SvOlli/sorbus/doc/site/jam/monitors.md

# Monitors

Not displays are meant here, but software that allows you to view and change
the content of memory. And most of the times, more.

## WozMon

Storage: in ROM

The most basic one, implemented originally in just 256 bytes for the Apple 1
Computer. Everything is entered and displayed as hex.

Available commands (examples):

- `0400`: dump the content of memory location $0400
- `0400 0404`: dump the content of memory locations $0400 and $0404
- `0400.0407`: dump the content of memory locations $0400 to $0407
- `0400: 9C`: write $9C to memory location $0400
- `0400: 9C 01 DF A0 00 00 09 60`: write the bytes to memory starting at $0400
- `0400R`: start the program $0400 (an alias `0400G` can be used as well)

A significant change to the Sorbus version of WozMon is that if a routine
started using the `R` command returns using the `RTS` opcode will drop you
back to WozMon. This is also the final ballback if everything else fails
(NMOS 6502 CPU installed and no software available on bootblock 2).

## TIM

TIM (Terminal Interface Monitor) is a small (1kB) program that was part of the
MOS 6530-004 chip. That chip was sold together with the first 6502 CPUs and
documentation on how to build a computer with this. Also this chip is used in
the Jolt Computer, which was the first computer sold based on the 6502.

The following descriptions lacks description of the paper tape and other I/O
routines, besides mentioning them.

Output: upon start you are typically greeted with

```txt
    ADDR P  A  X  Y  S
 *  E619 33 28 00 00 FF
.
```

The first line is an addition by the Sorbus version of TIM to help
understanding the output below:

- The first char indicates the kind of interrupt that occured:
  - ` ` (space): BRK instruction (BRK #$00 on Sorbus, since it's implemented
    as a two byte instruction
  - `#` (hash): NMI triggered via $FFFA/$FFFB
  - `%` (percent): IRQ triggered via $FFFE/$FFFF (Sorbus extension)
- `*` always printed
- ADDR: current address. The monitor is typically triggered by an interrupt.
- P: processor flags
- A: accumulator
- X: index register X
- Y: index register Y
- S: stack pointer (full stack pointer value is $01xx)

The following dot (`.`) is the input prompt. Note that there is no backspace
available. The input needs to be canceled and then start anew.

Available commands:

- `M`: dump 8 bytes of memory
- `R`: dump registers (the line described above)
- `:`: change the former output data
- `G`: go to the address shown in ADDR
- `L`, `W`, `H`: these are related to paper tape
- `V`: enables/disables verify for the `LH` command

So jumping to a specific address is handled by first running `R`, then changing
the ADDR with `:` (you can skip the rest by pressing return), and finally jump
using `G`. However, to return to the monitor you have to invoke it again using
the `BRK $00` opcode, `RTS` will not work here, like it did in WozMon.

A more detailed documentation is at the start of the
TIM source code (src/65c02/jam/rom/tim.s). The following is a revised version.

```txt
PROMPTING CHARACTER IS A PERIOD (.)
-----------------------------------

DISPLAY COMMANDS
----------------

.R                   DISPLAY REGISTERS (PC,F,A,X,Y,SP)
.M  ADDR             DISPLAY MEMORY ( 8 BYTES BEGINNING AT ADDR )

ALTER COMMAND (:)
-----------------
.:  DATA             ALTERS PREVIOUSLY DISPLAYED ITEM OR NEXT ITEM

PAPER TAPE I/O COMMANDS
------------------------

.LH                  LOAD HEX TAPE
.WB ADDR1 ADDR2      WRITE BNPF TAPE (FROM LOW ADDR1 TO HIGH ADDR2)
.WH ADDR1 ADDR2      WRITE HEX TAPE (FROM LOW ADDR1 TO HIGH ADDR2)

CONTROL COMMANDS
----------------

.G                   GO, CONTINUE EXECUTION FROM CIRRENT PC ADDRESS

.V                   TOGGLES VERIFY OPTION (DEFAULT: OFF)
                        (IF ITS ON, TURNS IT OFF; IF OFF, TURNS ON)

BRK AND NMI ENTRY POINTS TO TIM
-------------------------------

    TIM IS NORMALLY ENTERED WHEN A 'BRK' INSTRUKTION IS
        ENCOUNTERED DURING PROGRAM EXECUTION.  AT THAT
        TIME CPU REGISTERS ARE OUTPUT:    PC F A X Y SP
        and   CONTROL   IS GIVEN TO THE KEYBOARD.

    USER MAY ENTER TIM BY PROGRAMMED BRK OR INDUCED NMI.  NMI
        ENTRIES CAUSE A '#' TO PRECEDE THE '.' IN THE CPU REGISTER
        PRINTOUT FORMAT

NON-BRK INTRO (EXTERNAL DEVICE) INTERRUPT HANDLING
--------------------------------------------------

    A NON-BRK INTRO INTERRUPT CAUSES AN INDIRECT JUMP TO THE ADDRESS
        LOCATED AT 'UINT' (HEX FFF8).  THIS LOCATION CAN BE SET
        USING THE ALTER CMD, OR LOADED AUTOMATICALLY IN PAPER TAPE
        FROM WITH THE LH CMD IF THE USER ASSIGNS HIS INTRO INTERRUPT
        VECTOR TO $FFF8 IN THE SOURCE ASSEMBLY PROGRAM.

    IF NOT RESET BY THE USER, UINT IS SET TO CAUSE EXTERNAL
        DEVICE INTERRUPTS TO ENTER TIM AS NMI'S.  I.E.,
        IF A NMI OCOURS WITHOUT AN INDUCED NMI SIGNAL, IT IS
        AN EXTERNAL DEVICE INTERRUPT.

    Note: This has been changed for Sorbus from FFF8 to DF7C (UBRK)

SETTING AND RESETTING PROGRAM BREAKPOINTS
-----------------------------------------

    BREAKPOINTS ARE SET AND RESET USING THE MEMORY DISPLAY
        AND ALTER COMMANDS.  BRK HAS A '00' OPERATION CODE.
    TO SET A BREAKPOINT SIMPLY DISPLAY THE MEMORY LOCATION
        (FIRST INSTRUCTION.byte) AT WHICH THE BREAKPOINT IS
        TO BE PLACED THEN ALTER THE LOCATION TO '00'.  THERE IS
        NO LIMIT TO THE NUMBER OF BREAKPOINTS THAT CAN BE
        ACTIVE AT ONE TIME.
    TO RESET A BREAKPOINT, RESTORE THE ALTERED MEMORY LOCATION
        TO ITS ORIGINAL VALUE.
    WHEN AND IF A BREAKPOINT IS ENCOUNTERED DURING EXECUTION,
        THE BREAKPOINT DATA PRECEDEC BY AN ':' IS DISPLAYED.
        THE PROGRAM COUNTER VALUE DISPLAYED IS THE BRK
        INSTRUCTION LOCATION + 1.
```

### Loading Software Via Papertape

Papertape was a common way of getting data into the first microcomputers.
Typically you set the machine into some kind of receiving mode and then
switched the input to the papertape. For the machine it was like someone
was typing in the data really fast.

Format of papertape data is:

```txt
;CCAAAADD[DD..]SSSS
```

Every character (except for the semicolon) stands for a hex digit.

| Byte | Function |
| ---- | --- |
| ; | indication of papertape data |
| CC | number of databytes sent later on, 00 indicates end of transmission |
| AAAA | address to write to |
| DD | a byte of data, number of bytes must match the number specified as CC |
| SSSS | checksum, every byte of CC, AA (2 bytes) and DD are added up and must match SSSS  |

The implementation is in TIM is rather fast. When using 32 bytes chunks
of data, you can load about 2kB per second.

## System Monitor of Apple //c (WozMon 2c)

Storage: as loadable program.

This monitor is a very enhanced version of the original WozMon, now
utilizing about 1.5k bytes without the help message. But for this it
comes with a lot of new features like a disassembler, a direct mini
assembler from the Apple //c and file access which is custom to the
Sorbus Computer.

As of now, this monitor needs to be loaded from the internal drive
using the file browser, because it's the monitor with the steepest
learning curve. It is just added to experience how cumbersome it is to
use this monitor.

Displaying and entering data works the same as on the original WozMon.
There is an addition: instead of entering hex data, you can also enter
ASCII by prepending the letter with a single quote (`'`). However, when
entering multiple data, make sure that every letter is prepended with a
quote, and also that the input is separated by spaces.

Furthermore, the `R` command has been renamed to `G` for "go".

All implemented commands (examples):

When the prompt is a asterisk (`*`):

- `0400`: dump the content of memory location $0400
- `0400 0404`: dump the content of memory locations $0400 and $0404
- `0400.0407`: dump the content of memory locations $0400 to $0407
- `0400: 9C`: write $9C to memory location $0400
- `0400: 9C 0D 03 A0 00 00 09 60`: write the bytes to memory starting at $0400
- `0410: 20 06 FF 'H 'e 'l 'l 'o 'r 'l 'd '! 00 60`:
   write a small program that outputs "Hellorld!". Greetings to Usage Electric.
- `0400G`: start the program $0400
- `50+50`: add those to hex values, getting $A0
- `30-22`: subtract those to hex values, getting $0E
- `R`: print out the CPU shadow registers of A, X, Y, P and SP. These will
   be read when using `G` and saved to then the program exists with an `RTS`
   opcode. (Option renamed from Ctrl-E.) The values of those registers can
   be changed by the `:` command as the edit address pointer has been put to
   the correct place in memory ($00FB-$00FF).
- `c000<0400.0bffM`: move (or rather copy) the memory from $0400 to $0BFF to
   $C000 to $C7FF.
- `c000<0400.0bffV`: verify (or rather compare) the memory from $0400 to
   $0BFF to $C000 to $C7FF.
- `bd<c000.cfffP`: put (or rather fill) the memory from $C000 to $CFFF with
   the value of $BD.
- `0400L`: list (or rather disassemble) 20 instructions starting at $0400.
- `!`: drop to the direct mini assembler (see below)
- `A$`: display the directory of the user id $A (10) (Sorbus extension)
- `A<1000{int-test.sx4`: load the file "int-test.sx4" from user id $A (10)
   to address $1000.
- `2<1000.1FFF}savetest.bin`: load the file "savetest.bin" from user id $2
   (2) from address $1000 to $1FFF, including.

When the prompt is an exclamation mark (`!`), the direct mini assembler is
running. Now the user input is evaluated like:

- `1000:stz $DF01`: assemble the instruction `STZ $DF01` to address $1000.
   (Note the `$` is optional.)
- ` rts`: assemble the instruction `RTS` to the now current address.
   ($1003 in this example, also note the mendatory leading space character
   for this case.)
- an empty input returns to the "asterisk input"

The supported instruction set is of the 65SC02. The BRK instruction is not
supporing an operand here, as it is used with the Sorbus JAM kernel.
