SvOlli/sorbus/doc/images/system_clock.png

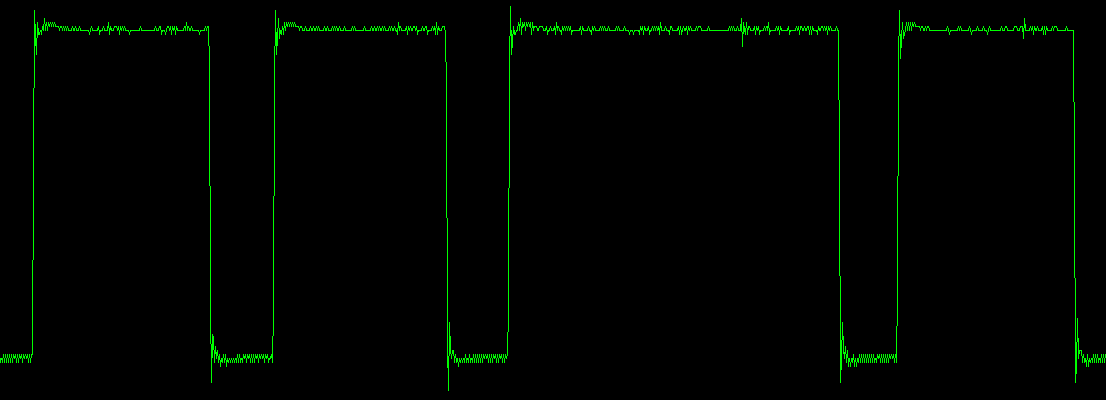
doc/images/system_clock.png
