SvOlli/sorbus/doc/site/images/SorbusPlant.jpg

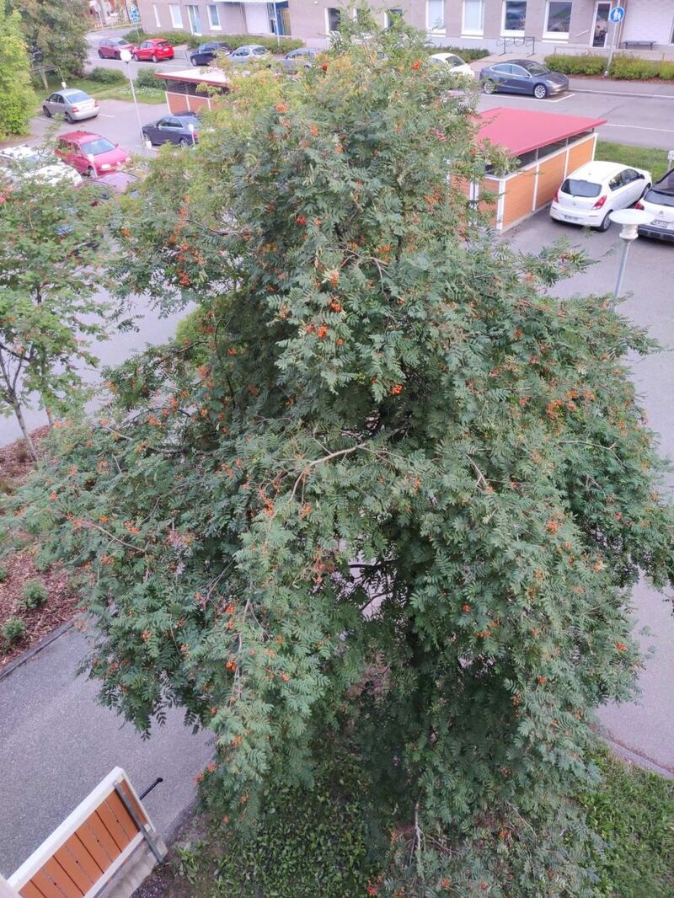
doc/site/images/SorbusPlant.jpg
