SvOlli/sorbus/src/rp2040/vga-term/pmhid.h

/*
 *  KEYCODE to Ascii Conversion
 *
 *  This file contains the various Keyboard Layout declaration supported by
 *  PicoTerm.
 *
 *  Expand to array of [128][3]
 *                       |   +-> (ascii without shift, ascii with shift, ascii with right alt)
 *                       +-----> HID_KEYCODE (0..127)
 *
 * Usage: example to convert ascii from keycode (key) and shift modifier (shift).
 * Here we assume key < 128 ( printable )
 *
 *  uint8_t const conv_table[128][2] =  { HID_KEYCODE_TO_ASCII };
 *  char ch = shift ? conv_table[chr][1] : conv_table[chr][0];
 *
*/

#ifndef _PM_HID_H_
#define _PM_HID_H_

#include "tusb_common.h"

// Choose the mapping @ "make" call (eg: make picoterm, make picoterm_US, make all)
// See CMakeLists.txt for more informations
// Copy and paste an existing mapping to make a new one, see the


#ifdef __cplusplus
 extern "C" {
#endif

#define SCANCODE_F1  0x3a
#define SCANCODE_F2  0x3b
#define SCANCODE_F3  0x3c
#define SCANCODE_F4  0x3d
#define SCANCODE_F5  0x3e
#define SCANCODE_F6  0x3f
#define SCANCODE_F7  0x40
#define SCANCODE_F8  0x41
#define SCANCODE_F9  0x42
#define SCANCODE_F10 0x43
#define SCANCODE_F11 0x44
#define SCANCODE_F12 0x45

#define SCANCODE_CURSOR_LEFT  0x50
#define SCANCODE_CURSOR_RIGHT 0x4F
#define SCANCODE_CURSOR_UP    0x52
#define SCANCODE_CURSOR_DOWN  0x51
#define SCANCODE_PAGE_DOWN    0x4E
#define SCANCODE_PAGE_UP      0x4B
#define SCANCODE_HOME         0x4A
#define SCANCODE_END          0x4D
#define SCANCODE_DEL          0x4C
#define SCANCODE_INS          0x49

// Define esc sequence for some special key-code
#define PM_ESC_SEQ_COUNT 10
#define PM_ESC_SEQ_MAX_LEN 4 /* max len of ESC SEQ (structure make 2 byte more per entry) */
/* Structure: scancode, len_of_sequence, sequence_bytes_(padded_with_NULL) */
#define PM_KEYCODE_TO_ESC_SEQ \
    { SCANCODE_CURSOR_LEFT  , 3, 0x1b,0x5b,0x44,0x00 } /* ESC[D */ , \
		{ SCANCODE_CURSOR_RIGHT , 3, 0x1b,0x5b,0x43,0x00 }, \
    { SCANCODE_CURSOR_UP    , 3, 0x1b,0x5b,0x41,0x00 }, \
    { SCANCODE_CURSOR_DOWN  , 3, 0x1b,0x5b,0x42,0x00 }, \
		{ SCANCODE_PAGE_DOWN    , 4, 0x1b,0x5b,0x36,0x7e } /* ESC[6~ */ , \
    { SCANCODE_PAGE_UP      , 4, 0x1b,0x5b,0x35,0x7e } /* ESC[5~ */ , \
		{ SCANCODE_HOME         , 4, 0x1b,0x5b,0x31,0x7e } /* ESC[1~ */ , \
		{ SCANCODE_END          , 4, 0x1b,0x5b,0x34,0x7e } /* ESC[4~ */ , \
		{ SCANCODE_DEL          , 4, 0x1b,0x5b,0x33,0x7e } /* ESC[3~ */ , \
		{ SCANCODE_INS          , 4, 0x1b,0x5b,0x32,0x7e } /* ESC[2~ */


//--------------------------------------------------------------------/
// US keyboard
//--------------------------------------------------------------------/


#ifdef LOCALISE_US
#define KEYMAP "US"
#define KEYMAP_REV 1
#define PM_KEYCODE_TO_ASCII    \
    {0     , 0     ,0 }, /* 0x00 */ \
    {0     , 0     ,0 }, /* 0x01 */ \
    {0     , 0     ,0 }, /* 0x02 */ \
    {0     , 0     ,0 }, /* 0x03 */ \
    {'a'   , 'A'   ,0 }, /* 0x04 */ \
    {'b'   , 'B'   ,0 }, /* 0x05 */ \
    {'c'   , 'C'   ,0 }, /* 0x06 */ \
    {'d'   , 'D'   ,0 }, /* 0x07 */ \
    {'e'   , 'E'   ,0 }, /* 0x08 */ \
    {'f'   , 'F'   ,0 }, /* 0x09 */ \
    {'g'   , 'G'   ,0 }, /* 0x0a */ \
    {'h'   , 'H'   ,0 }, /* 0x0b */ \
    {'i'   , 'I'   ,0 }, /* 0x0c */ \
    {'j'   , 'J'   ,0 }, /* 0x0d */ \
    {'k'   , 'K'   ,0 }, /* 0x0e */ \
    {'l'   , 'L'   ,0 }, /* 0x0f */ \
    {'m'   , 'M'   ,0 }, /* 0x10 */ \
    {'n'   , 'N'   ,0 }, /* 0x11 */ \
    {'o'   , 'O'   ,0 }, /* 0x12 */ \
    {'p'   , 'P'   ,0 }, /* 0x13 */ \
    {'q'   , 'Q'   ,0 }, /* 0x14 */ \
    {'r'   , 'R'   ,0 }, /* 0x15 */ \
    {'s'   , 'S'   ,0 }, /* 0x16 */ \
    {'t'   , 'T'   ,0 }, /* 0x17 */ \
    {'u'   , 'U'   ,0 }, /* 0x18 */ \
    {'v'   , 'V'   ,0 }, /* 0x19 */ \
    {'w'   , 'W'   ,0 }, /* 0x1a */ \
    {'x'   , 'X'   ,0 }, /* 0x1b */ \
    {'y'   , 'Y'   ,0 }, /* 0x1c */ \
    {'z'   , 'Z'   ,0 }, /* 0x1d */ \
    {'1'   , '!'   ,0 }, /* 0x1e */ \
    {'2'   , '@'   ,0 }, /* 0x1f */ \
    {'3'   , '#'   ,0 }, /* 0x20 */ \
    {'4'   , '$'   ,0 }, /* 0x21 */ \
    {'5'   , '%'   ,0 }, /* 0x22 */ \
    {'6'   , '^'   ,0 }, /* 0x23 */ \
    {'7'   , '&'   ,0 }, /* 0x24 */ \
    {'8'   , '*'   ,0 }, /* 0x25 */ \
    {'9'   , '('   ,0 }, /* 0x26 */ \
    {'0'   , ')'   ,0 }, /* 0x27 */ \
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
    {'\b'  , '\b'  ,0 }, /* 0x2a Backspace */ \
    {'\t'  , '\t'  ,0 }, /* 0x2b */ \
    {' '   , ' '   ,0 }, /* 0x2c */ \
    {'-'   , '_'   ,0 }, /* 0x2d */ \
    {'='   , '+'   ,0 }, /* 0x2e */ \
    {'['   , '{'   ,0 }, /* 0x2f */ \
    {']'   , '}'   ,0 }, /* 0x30 */ \
    {'\\'  , '|'   ,0 }, /* 0x31 */ \
    {'#'   , '~'   ,0 }, /* 0x32 */ \
    {';'   , ':'   ,0 }, /* 0x33 */ \
    {'\''  , '\"'  ,0 }, /* 0x34 */ \
    {'`'   , '~'   ,0 }, /* 0x35 */ \
    {','   , '<'   ,0 }, /* 0x36 */ \
    {'.'   , '>'   ,0 }, /* 0x37 */ \
    {'/'   , '?'   ,0 }, /* 0x38 */ \
                                  \
    {0     , 0     ,0 }, /* 0x39 */ \
    {0     , 0     ,0 }, /* 0x3a */ \
    {0     , 0     ,0 }, /* 0x3b */ \
    {0     , 0     ,0 }, /* 0x3c */ \
    {0     , 0     ,0 }, /* 0x3d */ \
    {0     , 0     ,0 }, /* 0x3e */ \
    {0     , 0     ,0 }, /* 0x3f */ \
    {0     , 0     ,0 }, /* 0x40 */ \
    {0     , 0     ,0 }, /* 0x41 */ \
    {0     , 0     ,0 }, /* 0x42 */ \
    {0     , 0     ,0 }, /* 0x43 */ \
    {0     , 0     ,0 }, /* 0x44 */ \
    {0     , 0     ,0 }, /* 0x45 */ \
    {0     , 0     ,0 }, /* 0x46 */ \
    {0     , 0     ,0 }, /* 0x47 */ \
    {0     , 0     ,0 }, /* 0x48 */ \
    {0x16     , 0     ,0 }, /* 0x49 INS   */ \
    {0        , 0     ,0 }, /* 0x4a       */ \
    {0x12     , 0     ,0 }, /* 0x4b PGUP  */ \
    {0x7f     , 0     ,0 }, /* 0x4c DEL   */ \
    {0        , 0     ,0 }, /* 0x4d       */ \
    {0x03     , 0     ,0 }, /* 0x4e PGDN  */ \
    {0x04     , 0     ,0 }, /* 0x4f RIGHT */ \
    {0x13     , 0     ,0 }, /* 0x50 LEFT  */ \
    {0x18     , 0     ,0 }, /* 0x51 DOWN  */ \
    {0x05     , 0     ,0 }, /* 0x52 UP    */ \
    {0        , 0     ,0 }, /* 0x53       */ \
                                  \
    {'/'   , '/'   ,0 }, /* 0x54 */ \
    {'*'   , '*'   ,0 }, /* 0x55 */ \
    {'-'   , '-'   ,0 }, /* 0x56 */ \
    {'+'   , '+'   ,0 }, /* 0x57 */ \
    {'\r'  , '\r'  ,0 }, /* 0x58 */ \
    {'1'   , 0     ,0 }, /* 0x59 */ \
    {'2'   , 0     ,0 }, /* 0x5a */ \
    {'3'   , 0     ,0 }, /* 0x5b */ \
    {'4'   , 0     ,0 }, /* 0x5c */ \
    {'5'   , '5'   ,0 }, /* 0x5d */ \
    {'6'   , 0     ,0 }, /* 0x5e */ \
    {'7'   , 0     ,0 }, /* 0x5f */ \
    {'8'   , 0     ,0 }, /* 0x60 */ \
    {'9'   , 0     ,0 }, /* 0x61 */ \
    {'0'   , 0     ,0 }, /* 0x62 */ \
    {'0'   , 0     ,0 }, /* 0x63 */ \
    {'='   , '='   ,0 }, /* 0x67 */ \

#endif


//--------------------------------------------------------------------/
// UK keyboard
//--------------------------------------------------------------------/


#ifdef LOCALISE_UK
#define KEYMAP "UK"
#define KEYMAP_REV 1
#define PM_KEYCODE_TO_ASCII    \
    {0     , 0     ,0 }, /* 0x00 */ \
    {0     , 0     ,0 }, /* 0x01 */ \
    {0     , 0     ,0 }, /* 0x02 */ \
    {0     , 0     ,0 }, /* 0x03 */ \
    {'a'   , 'A'   ,0 }, /* 0x04 */ \
    {'b'   , 'B'   ,0 }, /* 0x05 */ \
    {'c'   , 'C'   ,0 }, /* 0x06 */ \
    {'d'   , 'D'   ,0 }, /* 0x07 */ \
    {'e'   , 'E'   ,0 }, /* 0x08 */ \
    {'f'   , 'F'   ,0 }, /* 0x09 */ \
    {'g'   , 'G'   ,0 }, /* 0x0a */ \
    {'h'   , 'H'   ,0 }, /* 0x0b */ \
    {'i'   , 'I'   ,0 }, /* 0x0c */ \
    {'j'   , 'J'   ,0 }, /* 0x0d */ \
    {'k'   , 'K'   ,0 }, /* 0x0e */ \
    {'l'   , 'L'   ,0 }, /* 0x0f */ \
    {'m'   , 'M'   ,0 }, /* 0x10 */ \
    {'n'   , 'N'   ,0 }, /* 0x11 */ \
    {'o'   , 'O'   ,0 }, /* 0x12 */ \
    {'p'   , 'P'   ,0 }, /* 0x13 */ \
    {'q'   , 'Q'   ,0 }, /* 0x14 */ \
    {'r'   , 'R'   ,0 }, /* 0x15 */ \
    {'s'   , 'S'   ,0 }, /* 0x16 */ \
    {'t'   , 'T'   ,0 }, /* 0x17 */ \
    {'u'   , 'U'   ,0 }, /* 0x18 */ \
    {'v'   , 'V'   ,0 }, /* 0x19 */ \
    {'w'   , 'W'   ,0 }, /* 0x1a */ \
    {'x'   , 'X'   ,0 }, /* 0x1b */ \
    {'y'   , 'Y'   ,0 }, /* 0x1c */ \
    {'z'   , 'Z'   ,0 }, /* 0x1d */ \
    {'1'   , '!'   ,0 }, /* 0x1e */ \
    {'2'   , '\"'  ,0 }, /* 0x1f */ \
    {'3'   , '#'   ,0 }, /* 0x20 */ \
    {'4'   , '$'   ,0 }, /* 0x21 */ \
    {'5'   , '%'   ,0 }, /* 0x22 */ \
    {'6'   , '^'   ,0 }, /* 0x23 */ \
    {'7'   , '&'   ,0 }, /* 0x24 */ \
    {'8'   , '*'   ,0 }, /* 0x25 */ \
    {'9'   , '('   ,0 }, /* 0x26 */ \
    {'0'   , ')'   ,0 }, /* 0x27 */ \
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
    {'\b'  , '\b'  ,0 }, /* 0x2a Backspace */ \
    {'\t'  , '\t'  ,0 }, /* 0x2b */ \
    {' '   , ' '   ,0 }, /* 0x2c */ \
    {'-'   , '_'   ,0 }, /* 0x2d */ \
    {'='   , '+'   ,0 }, /* 0x2e */ \
    {'['   , '{'   ,0 }, /* 0x2f */ \
    {']'   , '}'   ,0 }, /* 0x30 */ \
    {'\\'  , '|'   ,0 }, /* 0x31 */ \
    {'#'   , '~'   ,0 }, /* 0x32 */ \
    {';'   , ':'   ,0 }, /* 0x33 */ \
    {'\''  , '@'   ,0 }, /* 0x34 */ \
    {'`'   , '~'   ,0 }, /* 0x35 */ \
    {','   , '<'   ,0 }, /* 0x36 */ \
    {'.'   , '>'   ,0 }, /* 0x37 */ \
    {'/'   , '?'   ,0 }, /* 0x38 */ \
                                  \
    {0     , 0     ,0 }, /* 0x39 */ \
    {0     , 0     ,0 }, /* 0x3a */ \
    {0     , 0     ,0 }, /* 0x3b */ \
    {0     , 0     ,0 }, /* 0x3c */ \
    {0     , 0     ,0 }, /* 0x3d */ \
    {0     , 0     ,0 }, /* 0x3e */ \
    {0     , 0     ,0 }, /* 0x3f */ \
    {0     , 0     ,0 }, /* 0x40 */ \
    {0     , 0     ,0 }, /* 0x41 */ \
    {0     , 0     ,0 }, /* 0x42 */ \
    {0     , 0     ,0 }, /* 0x43 */ \
    {0     , 0     ,0 }, /* 0x44 */ \
    {0     , 0     ,0 }, /* 0x45 */ \
    {0     , 0     ,0 }, /* 0x46 */ \
    {0     , 0     ,0 }, /* 0x47 */ \
    {0     , 0     ,0 }, /* 0x48 */ \
    {0x16     , 0     ,0 }, /* 0x49 INS   */ \
    {0        , 0     ,0 }, /* 0x4a       */ \
    {0x12     , 0     ,0 }, /* 0x4b PGUP  */ \
    {0x7f     , 0     ,0 }, /* 0x4c DEL   */ \
    {0        , 0     ,0 }, /* 0x4d       */ \
    {0x03     , 0     ,0 }, /* 0x4e PGDN  */ \
    {0x04     , 0     ,0 }, /* 0x4f RIGHT */ \
    {0x13     , 0     ,0 }, /* 0x50 LEFT  */ \
    {0x18     , 0     ,0 }, /* 0x51 DOWN  */ \
    {0x05     , 0     ,0 }, /* 0x52 UP    */ \
    {0        , 0     ,0 }, /* 0x53       */ \
                                  \
    {'/'   , '/'   ,0 }, /* 0x54 */ \
    {'*'   , '*'   ,0 }, /* 0x55 */ \
    {'-'   , '-'   ,0 }, /* 0x56 */ \
    {'+'   , '+'   ,0 }, /* 0x57 */ \
    {'\r'  , '\r'  ,0 }, /* 0x58 */ \
    {'1'   , 0     ,0 }, /* 0x59 */ \
    {'2'   , 0     ,0 }, /* 0x5a */ \
    {'3'   , 0     ,0 }, /* 0x5b */ \
    {'4'   , 0     ,0 }, /* 0x5c */ \
    {'5'   , '5'   ,0 }, /* 0x5d */ \
    {'6'   , 0     ,0 }, /* 0x5e */ \
    {'7'   , 0     ,0 }, /* 0x5f */ \
    {'8'   , 0     ,0 }, /* 0x60 */ \
    {'9'   , 0     ,0 }, /* 0x61 */ \
    {'0'   , 0     ,0 }, /* 0x62 */ \
    {'0'   , 0     ,0 }, /* 0x63 */ \
    {'\\'  , '|'   ,0 }, /* 0x64 */ \
    {'0'   , 0     ,0 }, /* 0x65 */ \
    {'0'   , 0     ,0 }, /* 0x66 */ \
    {'='   , '='   ,0 }, /* 0x67 */ \

#endif



 //--------------------------------------------------------------------/
 // DE keyboard
 //
 // third column is ALT GR modification
 //--------------------------------------------------------------------/


 #ifdef LOCALISE_DE
 #define KEYMAP "DE"
 #define KEYMAP_REV 2
 #define PM_KEYCODE_TO_ASCII    \
     {0     , 0     ,0 }, /* 0x00 */ \
     {0     , 0     ,0 }, /* 0x01 */ \
     {0     , 0     ,0 }, /* 0x02 */ \
     {0     , 0     ,0 }, /* 0x03 */ \
     {'a'   , 'A'   ,0 }, /* 0x04 */ \
     {'b'   , 'B'   ,0 }, /* 0x05 */ \
     {'c'   , 'C'   ,0 }, /* 0x06 */ \
     {'d'   , 'D'   ,0 }, /* 0x07 */ \
     {'e'   , 'E'   ,0 }, /* 0x08 */ \
     {'f'   , 'F'   ,0 }, /* 0x09 */ \
     {'g'   , 'G'   ,0 }, /* 0x0a */ \
     {'h'   , 'H'   ,0 }, /* 0x0b */ \
     {'i'   , 'I'   ,0 }, /* 0x0c */ \
     {'j'   , 'J'   ,0 }, /* 0x0d */ \
     {'k'   , 'K'   ,0 }, /* 0x0e */ \
     {'l'   , 'L'   ,0 }, /* 0x0f */ \
     {'m'   , 'M'   ,0 }, /* 0x10 */ \
     {'n'   , 'N'   ,0 }, /* 0x11 */ \
     {'o'   , 'O'   ,0 }, /* 0x12 */ \
     {'p'   , 'P'   ,0 }, /* 0x13 */ \
     {'q'   , 'Q'   ,'@' }, /* 0x14 */ \
     {'r'   , 'R'   ,0 }, /* 0x15 */ \
     {'s'   , 'S'   ,0 }, /* 0x16 */ \
     {'t'   , 'T'   ,0 }, /* 0x17 */ \
     {'u'   , 'U'   ,0 }, /* 0x18 */ \
     {'v'   , 'V'   ,0 }, /* 0x19 */ \
     {'w'   , 'W'   ,0 }, /* 0x1a */ \
     {'x'   , 'X'   ,0 }, /* 0x1b */ \
     {'z'   , 'Z'   ,0 }, /* 0x1c */ \
     {'y'   , 'Y'   ,0 }, /* 0x1d */ \
     {'1'   , '!'   ,0 }, /* 0x1e */ \
     {'2'   , '\"'  ,0 }, /* 0x1f */ \
     {'3'   , 0     ,0 }, /* 0x20 */ \
     {'4'   , '$'   ,0 }, /* 0x21 */ \
     {'5'   , '%'   ,0 }, /* 0x22 */ \
     {'6'   , '&'   ,0 }, /* 0x23 */ \
     {'7'   , '/'   ,'{' }, /* 0x24 */ \
     {'8'   , '('   ,'[' }, /* 0x25 */ \
     {'9'   , ')'   ,']' }, /* 0x26 */ \
     {'0'   , '='   ,'}' }, /* 0x27 */ \
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
     {'\b'  , '\b'  ,0 }, /* 0x2a  Backspace */ \
     {'\t'  , '\t'  ,0 }, /* 0x2b */ \
     {' '   , ' '   ,0 }, /* 0x2c */ \
     { 0    , '?'   ,'\\' }, /* 0x2d  ß */ \
     {','   , '\''  ,0 }, /* 0x2e */ \
     { 0    , 0     ,0 }, /* 0x2f */ \
     {'+'   , '*'   ,'~' }, /* 0x30 */ \
     {'#'   , '\''   ,0 }, /* 0x31 */ \
     {'#'   , '\''   ,0 }, /* 0x32 */ \
     { 0    , 0     ,0 }, /* 0x33 */ \
     { 0    , 0     ,0 }, /* 0x34 */ \
     {'`'   , '~'   ,0 }, /* 0x35 */ \
     {','   , ';'   ,0 }, /* 0x36 */ \
     {'.'   , ':'   ,0 }, /* 0x37 */ \
     {'-'   , '_'   ,0 }, /* 0x38 */ \
                                   \
     {0     , 0     ,0 }, /* 0x39 */ \
     {0     , 0     ,0 }, /* 0x3a */ \
     {0     , 0     ,0 }, /* 0x3b */ \
     {0     , 0     ,0 }, /* 0x3c */ \
     {0     , 0     ,0 }, /* 0x3d */ \
     {0     , 0     ,0 }, /* 0x3e */ \
     {0     , 0     ,0 }, /* 0x3f */ \
     {0     , 0     ,0 }, /* 0x40 */ \
     {0     , 0     ,0 }, /* 0x41 */ \
     {0     , 0     ,0 }, /* 0x42 */ \
     {0     , 0     ,0 }, /* 0x43 */ \
     {0     , 0     ,0 }, /* 0x44 */ \
     {0     , 0     ,0 }, /* 0x45 */ \
     {0     , 0     ,0 }, /* 0x46 */ \
     {0     , 0     ,0 }, /* 0x47 */ \
     {0     , 0     ,0 }, /* 0x48 */ \
    {0x16     , 0     ,0 }, /* 0x49 INS   */ \
    {0        , 0     ,0 }, /* 0x4a       */ \
    {0x12     , 0     ,0 }, /* 0x4b PGUP  */ \
    {0x7f     , 0     ,0 }, /* 0x4c DEL   */ \
    {0        , 0     ,0 }, /* 0x4d       */ \
    {0x03     , 0     ,0 }, /* 0x4e PGDN  */ \
    {0x04     , 0     ,0 }, /* 0x4f RIGHT */ \
    {0x13     , 0     ,0 }, /* 0x50 LEFT  */ \
    {0x18     , 0     ,0 }, /* 0x51 DOWN  */ \
    {0x05     , 0     ,0 }, /* 0x52 UP    */ \
    {0        , 0     ,0 }, /* 0x53       */ \
                                   \
     {'/'   , '/'   ,0 }, /* 0x54 */ \
     {'*'   , '*'   ,0 }, /* 0x55 */ \
     {'-'   , '-'   ,0 }, /* 0x56 */ \
     {'+'   , '+'   ,0 }, /* 0x57 */ \
     {'\r'  , '\r'  ,0 }, /* 0x58 */ \
     {'1'   , 0     ,0 }, /* 0x59 */ \
     {'2'   , 0     ,0 }, /* 0x5a */ \
     {'3'   , 0     ,0 }, /* 0x5b */ \
     {'4'   , 0     ,0 }, /* 0x5c */ \
     {'5'   , '5'   ,0 }, /* 0x5d */ \
     {'6'   , 0     ,0 }, /* 0x5e */ \
     {'7'   , 0     ,0 }, /* 0x5f */ \
     {'8'   , 0     ,0 }, /* 0x60 */ \
     {'9'   , 0     ,0 }, /* 0x61 */ \
     {'0'   , 0     ,0 }, /* 0x62 */ \
     {'.'   , 0     ,0 }, /* 0x63 */ \
     {'<'  , '>'   ,'|' }, /* 0x64 */ \
     {'0'   , 0     ,0 }, /* 0x65 */ \
     {'0'   , 0     ,0 }, /* 0x66 */ \
     {'='   , '='   ,0 }, /* 0x67 */ \

 #endif

 //--------------------------------------------------------------------/
 // FR keyboard
 //
 // third column is ALT GR modification
 //--------------------------------------------------------------------/
 // 18 nov  2022: FR layout fix for "[" + AltGr fixed.
 // 25 sept 2022: FR layout doen't capture AltGR combination.
 //              characters [,],{,},|,@,\ are temporarily duplicated from F1 to F7.

 #ifdef LOCALISE_FR
 #define KEYMAP "FR"
 #define KEYMAP_REV 2
 #define PM_KEYCODE_TO_ASCII    \
     {0     , 0     ,0 }, /* 0x00 */ \
     {0     , 0     ,0 }, /* 0x01 */ \
     {0     , 0     ,0 }, /* 0x02 */ \
     {0     , 0     ,0 }, /* 0x03 */ \
     {'q'   , 'Q'   ,0 }, /* 0x04 */ \
     {'b'   , 'B'   ,0 }, /* 0x05 */ \
     {'c'   , 'C'   ,0 }, /* 0x06 */ \
     {'d'   , 'D'   ,0 }, /* 0x07 */ \
     {'e'   , 'E'   ,0 }, /* 0x08 (alt=EUR)*/ \
     {'f'   , 'F'   ,0 }, /* 0x09 */ \
     {'g'   , 'G'   ,0 }, /* 0x0a */ \
     {'h'   , 'H'   ,0 }, /* 0x0b */ \
     {'i'   , 'I'   ,0 }, /* 0x0c */ \
     {'j'   , 'J'   ,0 }, /* 0x0d */ \
     {'k'   , 'K'   ,0 }, /* 0x0e */ \
     {'l'   , 'L'   ,0 }, /* 0x0f */ \
     {','   , '?'   ,0 }, /* 0x10 */ \
     {'n'   , 'N'   ,0 }, /* 0x11 */ \
     {'o'   , 'O'   ,0 }, /* 0x12 */ \
     {'p'   , 'P'   ,0 }, /* 0x13 */ \
     {'a'   , 'A'   ,'@' }, /* 0x14 */ \
     {'r'   , 'R'   ,0 }, /* 0x15 */ \
     {'s'   , 'S'   ,0 }, /* 0x16 */ \
     {'t'   , 'T'   ,0 }, /* 0x17 */ \
     {'u'   , 'U'   ,0 }, /* 0x18 */ \
     {'v'   , 'V'   ,0 }, /* 0x19 */ \
     {'z'   , 'Z'   ,0 }, /* 0x1a */ \
     {'x'   , 'X'   ,0 }, /* 0x1b */ \
     {'y'   , 'Y'   ,0 }, /* 0x1c */ \
     {'w'   , 'W'   ,0 }, /* 0x1d */ \
     {'&'   , '1'   ,0 }, /* 0x1e */ \
     {'e'   , '2'   ,'~' }, /* 0x1f =é */ \
     {'\"'  , '3'   ,'#' }, /* 0x20 */ \
     {'\''  , '4'   ,'{' }, /* 0x21 */ \
     {'('   , '5'   ,'[' }, /* 0x22 */ \
     {'-'   , '6'   ,'|' }, /* 0x23 */ \
     {'e'   , '7'   ,'`' }, /* 0x24 =è */ \
     {'_'   , '8'   ,'\\' }, /* 0x25 */ \
     {'c'   , '9'   ,'^' }, /* 0x26 =ç */ \
     {'a'   , '0'   ,'@' }, /* 0x27 =à */ \
     {'\r'  , '\r'  ,0 }, /* 0x28 */ \
     {'\x1b', '\x1b',0 }, /* 0x29 */ \
     {'\b'  , '\b'  ,0 }, /* 0x2a Backspace */ \
     {'\t'  , '\t'  ,0 }, /* 0x2b */ \
     {' '   , ' '   ,0 }, /* 0x2c */ \
     {')'   , 0    ,']' }, /* 0x2d shift=° */ \
     {'='   , '+'  ,'}'}, /* 0x2e */ \
     {'^'   , 0    ,0 }, /* 0x2f shift=tréma(named Diaeresis in english) */ \
     {'$'   , '&'   ,0 }, /* 0x30 alt=crossed_circle*/ \
     {'#'   , '\''  ,0 }, /* 0x31 */ \
     {'*'   , 'u'   ,0 }, /* 0x32 (on right of $34, shift=µ)*/ \
     {'m'   , 'M'   ,0 }, /* 0x33 */ \
     {'u'   , '%'   ,0 }, /* 0x34 ù */ \
     {'`'   , '~'   ,0 }, /* 0x35 (not correct but changed!)*/ \
     {';'   , '.'   ,0 }, /* 0x36 */ \
     {':'   , '/'   ,0 }, /* 0x37 */ \
     {'!'   , '!'   ,0 }, /* 0x38 shift=§*/ \
                                   \
     {0     , 0     ,0 }, /* 0x39 */ \
     {'['   , 0     ,0 }, /* 0x3a F1 */ \
     {']'   , 0     ,0 }, /* 0x3b F2 */ \
     {'{'   , 0     ,0 }, /* 0x3c F3 */ \
     {'}'   , 0     ,0 }, /* 0x3d F4 */ \
     {'|'   , 0     ,0 }, /* 0x3e F5 */ \
     {'@'   , 0     ,0 }, /* 0x3f F6 */ \
     {'\\'  , 0     ,0 }, /* 0x40 F7 */ \
     {'#'   , 0     ,0 }, /* 0x41 F8 */ \
     {0     , 0     ,0 }, /* 0x42 F9 */ \
     {0     , 0     ,0 }, /* 0x43 F10 */ \
     {0     , 0     ,0 }, /* 0x44 F11 */ \
     {0     , 0     ,0 }, /* 0x45 F12 */ \
     {0     , 0     ,0 }, /* 0x46 Print Screen*/ \
     {0     , 0     ,0 }, /* 0x47 Scroll Lock */ \
     {0     , 0     ,0 }, /* 0x48 Pause */ \
    {0x16     , 0     ,0 }, /* 0x49 INS   */ \
    {0        , 0     ,0 }, /* 0x4a       */ \
    {0x12     , 0     ,0 }, /* 0x4b PGUP  */ \
    {0x7f     , 0     ,0 }, /* 0x4c DEL   */ \
    {0        , 0     ,0 }, /* 0x4d       */ \
    {0x03     , 0     ,0 }, /* 0x4e PGDN  */ \
    {0x04     , 0     ,0 }, /* 0x4f RIGHT */ \
    {0x13     , 0     ,0 }, /* 0x50 LEFT  */ \
    {0x18     , 0     ,0 }, /* 0x51 DOWN  */ \
    {0x05     , 0     ,0 }, /* 0x52 UP    */ \
    {0        , 0     ,0 }, /* 0x53       */ \
                                   \
     {'/'   , '/'   ,0 }, /* 0x54 */ \
     {'*'   , '*'   ,0 }, /* 0x55 */ \
     {'-'   , '-'   ,0 }, /* 0x56 */ \
     {'+'   , '+'   ,0 }, /* 0x57 */ \
     {'\r'  , '\r'  ,0 }, /* 0x58 */ \
     {'1'   , 0     ,0 }, /* 0x59 */ \
     {'2'   , 0     ,0 }, /* 0x5a */ \
     {'3'   , 0     ,0 }, /* 0x5b */ \
     {'4'   , 0     ,0 }, /* 0x5c */ \
     {'5'   , '5'   ,0 }, /* 0x5d */ \
     {'6'   , 0     ,0 }, /* 0x5e */ \
     {'7'   , 0     ,0 }, /* 0x5f */ \
     {'8'   , 0     ,0 }, /* 0x60 */ \
     {'9'   , 0     ,0 }, /* 0x61 */ \
     {'0'   , 0     ,0 }, /* 0x62 */ \
     {'.'   , 0     ,0 }, /* 0x63 */ \
     {'<'  , '>'   ,'|' }, /* 0x64 */ \
     {'0'   , 0     ,0 }, /* 0x65 Menu */ \
     {'0'   , 0     ,0 }, /* 0x66 */ \
     {'='   , '='   ,0 }, /* 0x67 */ \

 #endif

 //--------------------------------------------------------------------/
 // BE keyboard
 //
 // third column is ALT GR modification
 //--------------------------------------------------------------------/
 // 25 sept 2022: FR layout doen't capture AltGR combination.
 //              characters [,],{,},|,@ are temporarily duplicated from F1 to F6.

 #ifdef LOCALISE_BE
 #define KEYMAP "BE"
 #define KEYMAP_REV 1
 #define PM_KEYCODE_TO_ASCII    \
     {0     , 0     ,0 }, /* 0x00 */ \
     {0     , 0     ,0 }, /* 0x01 */ \
     {0     , 0     ,0 }, /* 0x02 */ \
     {0     , 0     ,0 }, /* 0x03 */ \
     {'q'   , 'Q'   ,0 }, /* 0x04 */ \
     {'b'   , 'B'   ,0 }, /* 0x05 */ \
     {'c'   , 'C'   ,0 }, /* 0x06 */ \
     {'d'   , 'D'   ,0 }, /* 0x07 */ \
     {'e'   , 'E'   ,0 }, /* 0x08 (alt=EUR)*/ \
     {'f'   , 'F'   ,0 }, /* 0x09 */ \
     {'g'   , 'G'   ,0 }, /* 0x0a */ \
     {'h'   , 'H'   ,0 }, /* 0x0b */ \
     {'i'   , 'I'   ,0 }, /* 0x0c */ \
     {'j'   , 'J'   ,0 }, /* 0x0d */ \
     {'k'   , 'K'   ,0 }, /* 0x0e */ \
     {'l'   , 'L'   ,0 }, /* 0x0f */ \
     {','   , '?'   ,0 }, /* 0x10 */ \
     {'n'   , 'N'   ,0 }, /* 0x11 */ \
     {'o'   , 'O'   ,0 }, /* 0x12 */ \
     {'p'   , 'P'   ,0 }, /* 0x13 */ \
     {'a'   , 'A'   ,'@' }, /* 0x14 */ \
     {'r'   , 'R'   ,0 }, /* 0x15 */ \
     {'s'   , 'S'   ,0 }, /* 0x16 */ \
     {'t'   , 'T'   ,0 }, /* 0x17 */ \
     {'u'   , 'U'   ,0 }, /* 0x18 */ \
     {'v'   , 'V'   ,0 }, /* 0x19 */ \
     {'z'   , 'Z'   ,0 }, /* 0x1a */ \
     {'x'   , 'X'   ,0 }, /* 0x1b */ \
     {'y'   , 'Y'   ,0 }, /* 0x1c */ \
     {'w'   , 'W'   ,0 }, /* 0x1d */ \
     {'&'   , '1'   ,0 }, /* 0x1e */ \
     {'e'   , '2'   ,'@' }, /* 0x1f =é */ \
     {'\"'  , '3'   ,'#' }, /* 0x20 */ \
     {'\''  , '4'   ,0   }, /* 0x21 */ \
     {'('   , '5'   ,0   }, /* 0x22 */ \
     { 0    , '6'   ,'^' }, /* 0x23 =§ */ \
     {'e'   , '7'   ,0   }, /* 0x24 =è */ \
     {'!'   , '8'   ,0   }, /* 0x25 */ \
     {'c'   , '9'   ,'{' }, /* 0x26 =ç */ \
     {'a'   , '0'   ,'}' }, /* 0x27 =à */ \
     {'\r'  , '\r'  ,0 }, /* 0x28 */ \
     {'\x1b', '\x1b',0 }, /* 0x29 */ \
     {'\b'  , '\b'  ,0 }, /* 0x2a Backspace */ \
     {'\t'  , '\t'  ,0 }, /* 0x2b */ \
     {' '   , ' '   ,0 }, /* 0x2c */ \
     {')'   , 0     ,0 }, /* 0x2d shift=°(degree sign) */ \
     {'-'   , '_'   ,0 }, /* 0x2e */ \
     {'^'   , 0     ,'[' }, /* 0x2f shift=tréma(named Diaeresis in english) */ \
     {'$'   , '*'   ,']' }, /* 0x30 */ \
     {'#'   , '\''  ,0 }, /* 0x31 */ \
     {'u'   , '&'   ,'`' }, /* 0x32 (on right of $34, =µ, shift=£)*/ \
     {'m'   , 'M'   ,0 }, /* 0x33 */ \
     {'u'   , '%'   ,'\'' }, /* 0x34 =ù */ \
     {'`'   , '~'   ,0 }, /* 0x35 (not correct but changed!)*/ \
     {';'   , '.'   ,0 }, /* 0x36 */ \
     {':'   , '/'   ,0 }, /* 0x37 */ \
     {'='   , '+'   ,'~' }, /* 0x38 shift=§*/ \
                                   \
     {0     , 0     ,0 }, /* 0x39 */ \
     {'['   , 0     ,0 }, /* 0x3a F1 */ \
     {']'   , 0     ,0 }, /* 0x3b F2 */ \
     {'{'   , 0     ,0 }, /* 0x3c F3 */ \
     {'}'   , 0     ,0 }, /* 0x3d F4 */ \
     {'|'   , 0     ,0 }, /* 0x3e F5 */ \
     {'@'   , 0     ,0 }, /* 0x3f F6 */ \
     {'\\'  , 0     ,0 }, /* 0x40 F7 */ \
     {'#'   , 0     ,0 }, /* 0x41 F8 */ \
     {0     , 0     ,0 }, /* 0x42 F9 */ \
     {0     , 0     ,0 }, /* 0x43 F10 */ \
     {0     , 0     ,0 }, /* 0x44 F11 */ \
     {0     , 0     ,0 }, /* 0x45 F12 */ \
     {0     , 0     ,0 }, /* 0x46 Print Screen*/ \
     {0     , 0     ,0 }, /* 0x47 Scroll Lock */ \
     {0     , 0     ,0 }, /* 0x48 Pause */ \
    {0x16     , 0     ,0 }, /* 0x49 INS   */ \
    {0        , 0     ,0 }, /* 0x4a       */ \
    {0x12     , 0     ,0 }, /* 0x4b PGUP  */ \
    {0x7f     , 0     ,0 }, /* 0x4c DEL   */ \
    {0        , 0     ,0 }, /* 0x4d       */ \
    {0x03     , 0     ,0 }, /* 0x4e PGDN  */ \
    {0x04     , 0     ,0 }, /* 0x4f RIGHT */ \
    {0x13     , 0     ,0 }, /* 0x50 LEFT  */ \
    {0x18     , 0     ,0 }, /* 0x51 DOWN  */ \
    {0x05     , 0     ,0 }, /* 0x52 UP    */ \
    {0        , 0     ,0 }, /* 0x53       */ \
                                   \
     {'/'   , '/'   ,0 }, /* 0x54 */ \
     {'*'   , '*'   ,0 }, /* 0x55 */ \
     {'-'   , '-'   ,0 }, /* 0x56 */ \
     {'+'   , '+'   ,0 }, /* 0x57 */ \
     {'\r'  , '\r'  ,0 }, /* 0x58 */ \
     {'1'   , 0     ,0 }, /* 0x59 */ \
     {'2'   , 0     ,0 }, /* 0x5a */ \
     {'3'   , 0     ,0 }, /* 0x5b */ \
     {'4'   , 0     ,0 }, /* 0x5c */ \
     {'5'   , '5'   ,0 }, /* 0x5d */ \
     {'6'   , 0     ,0 }, /* 0x5e */ \
     {'7'   , 0     ,0 }, /* 0x5f */ \
     {'8'   , 0     ,0 }, /* 0x60 */ \
     {'9'   , 0     ,0 }, /* 0x61 */ \
     {'0'   , 0     ,0 }, /* 0x62 */ \
     {'.'   , 0     ,0 }, /* 0x63 */ \
     {'<'  , '>'   ,'\\' }, /* 0x64 */ \
     {'0'   , 0     ,0 }, /* 0x65 Menu */ \
     {'0'   , 0     ,0 }, /* 0x66 */ \
     {'='   , '='   ,0 }, /* 0x67 */ \

 #endif


#ifdef __cplusplus
 }
#endif

#endif /* _TUSB_HID_H__ */

/// @}
