SvOlli/sorbus/src/rp2040/fb32x32/translation_matrix_1.c

const unsigned int translation_matrix[0x0400] = {
   0x200,0x220,0x240,0x260,0x280,0x2a0,0x2c0,0x2e0,0x300,0x320,0x340,0x360,0x380,0x3a0,0x3c0,0x3e0,0x3e1,0x3c1,0x3a1,0x381,0x361,0x341,0x321,0x301,0x2e1,0x2c1,0x2a1,0x281,0x261,0x241,0x221,0x201,
   0x202,0x222,0x242,0x262,0x282,0x2a2,0x2c2,0x2e2,0x302,0x322,0x342,0x362,0x382,0x3a2,0x3c2,0x3e2,0x3e3,0x3c3,0x3a3,0x383,0x363,0x343,0x323,0x303,0x2e3,0x2c3,0x2a3,0x283,0x263,0x243,0x223,0x203,
   0x204,0x224,0x244,0x264,0x284,0x2a4,0x2c4,0x2e4,0x304,0x324,0x344,0x364,0x384,0x3a4,0x3c4,0x3e4,0x3e5,0x3c5,0x3a5,0x385,0x365,0x345,0x325,0x305,0x2e5,0x2c5,0x2a5,0x285,0x265,0x245,0x225,0x205,
   0x206,0x226,0x246,0x266,0x286,0x2a6,0x2c6,0x2e6,0x306,0x326,0x346,0x366,0x386,0x3a6,0x3c6,0x3e6,0x3e7,0x3c7,0x3a7,0x387,0x367,0x347,0x327,0x307,0x2e7,0x2c7,0x2a7,0x287,0x267,0x247,0x227,0x207,
   0x208,0x228,0x248,0x268,0x288,0x2a8,0x2c8,0x2e8,0x308,0x328,0x348,0x368,0x388,0x3a8,0x3c8,0x3e8,0x3e9,0x3c9,0x3a9,0x389,0x369,0x349,0x329,0x309,0x2e9,0x2c9,0x2a9,0x289,0x269,0x249,0x229,0x209,
   0x20a,0x22a,0x24a,0x26a,0x28a,0x2aa,0x2ca,0x2ea,0x30a,0x32a,0x34a,0x36a,0x38a,0x3aa,0x3ca,0x3ea,0x3eb,0x3cb,0x3ab,0x38b,0x36b,0x34b,0x32b,0x30b,0x2eb,0x2cb,0x2ab,0x28b,0x26b,0x24b,0x22b,0x20b,
   0x20c,0x22c,0x24c,0x26c,0x28c,0x2ac,0x2cc,0x2ec,0x30c,0x32c,0x34c,0x36c,0x38c,0x3ac,0x3cc,0x3ec,0x3ed,0x3cd,0x3ad,0x38d,0x36d,0x34d,0x32d,0x30d,0x2ed,0x2cd,0x2ad,0x28d,0x26d,0x24d,0x22d,0x20d,
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
   0x1e5,0x1c5,0x1a5,0x185,0x165,0x145,0x125,0x105,0x0e5,0x0c5,0x0a5,0x085,0x065,0x045,0x025,0x005,0x004,0x024,0x044,0x064,0x084,0x0a4,0x0c4,0x0e4,0x104,0x124,0x144,0x164,0x184,0x1a4,0x1c4,0x1e4,
   0x1e3,0x1c3,0x1a3,0x183,0x163,0x143,0x123,0x103,0x0e3,0x0c3,0x0a3,0x083,0x063,0x043,0x023,0x003,0x002,0x022,0x042,0x062,0x082,0x0a2,0x0c2,0x0e2,0x102,0x122,0x142,0x162,0x182,0x1a2,0x1c2,0x1e2,
   0x1e1,0x1c1,0x1a1,0x181,0x161,0x141,0x121,0x101,0x0e1,0x0c1,0x0a1,0x081,0x061,0x041,0x021,0x001,0x000,0x020,0x040,0x060,0x080,0x0a0,0x0c0,0x0e0,0x100,0x120,0x140,0x160,0x180,0x1a0,0x1c0,0x1e0
};
