SvOlli/sorbus/src/rp2040/common/cpu_detect.c

/**
 * Copyright (c) 2023-2024 SvOlli
 *
 * SPDX-License-Identifier: GPL-3.0-or-later
 */

#include "cpu_detect.h"
#include "bus.h"
#include <string.h>
#include <stdio.h>

#include "cpudetect.h"
#include "da_trace.h"

#define CYCLES_TOTAL (256)
#define SHOW_RAW_DUMP_IN_DEBUG 0

static uint32_t *last_trace = 0;
cputype_t cputype = 0;


uint32_t *cpu_detect_trace()
{
   return last_trace;
}


void cpu_detect_trace_free()
{
   ht_free( last_trace );
   last_trace = 0;
}


void cpu_detect( bool debug )
{
   uint32_t  trace[CYCLES_TOTAL] = { 0 };
   uint32_t  state;
   uint32_t  address;
   uint32_t  cycles_left_reset = 8;
   uint32_t  cycles_run = 0;
   bool      reset_done = false;
   uint8_t   memory[0x20] = { 0 };
   char      text[128] = { 0 };
   char      *b;
   int       bsize;
   int       used;

   memcpy( &memory[0], &cpudetect[0], sizeof(memory) );
   memset( &trace[0], 0, sizeof(trace) );

   // set lines to required state
   gpio_set_mask( bus_config.mask_rdy | bus_config.mask_irq | bus_config.mask_nmi );
   for( cycles_run = 0;
        (0x00 == memory[sizeof(memory)-1]) && (cycles_run < (CYCLES_TOTAL-1));
        ++cycles_run )
   {
      if( cycles_left_reset )
      {
         --cycles_left_reset;
         gpio_clr_mask( bus_config.mask_reset );
      }
      else
      {
         gpio_set_mask( bus_config.mask_reset );
      }

      // done: wait for things to settle and set clock to high
      sleep_us( 10 );
      gpio_set_mask( bus_config.mask_clock );
      // another delay before reading the bus, without it worked _most_ of the times
      sleep_us( 2 );

      // bus should be still valid from clock low
      state = gpio_get_all();
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
